Eco-Tec/FrosTool/3D-Model/Node/Case_FrossTool.fcstd

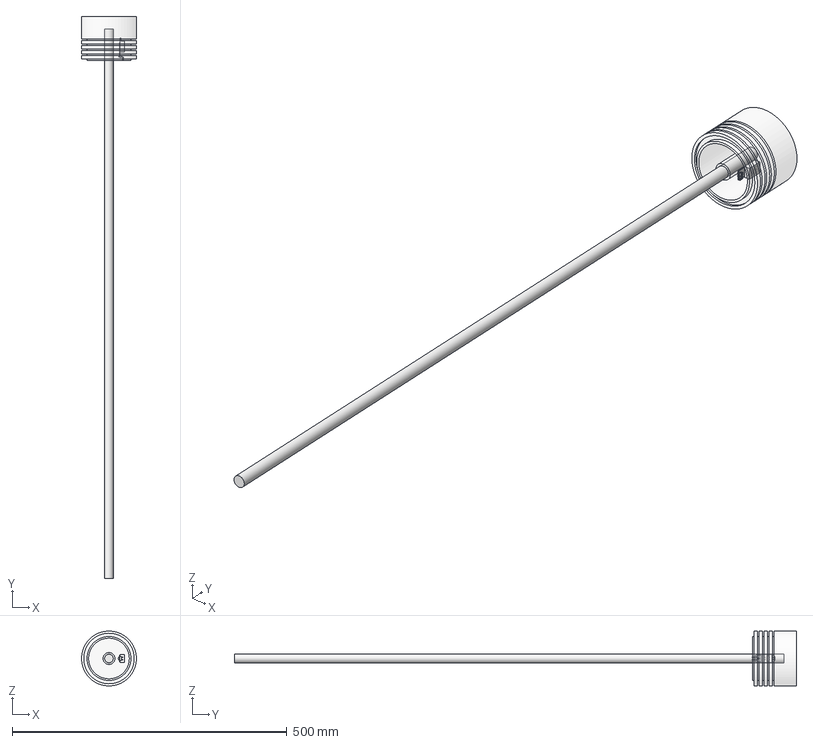
[picture p17: CAD file, 2017-10-28]
3D-Model/Node/Case_FrossTool.fcstd
99.9 x 1023.0 x 100.0 mm
DHT22-by_Gistroy
Tubo 1/2
case1
