Eco-Tec/FrosTool/3D-Model/Parts/Broker/orange-pi-zero-v1-1-1-carly_mx.2/Orange Pi Zero v1_1/parts/PLS-01.SLDPRT

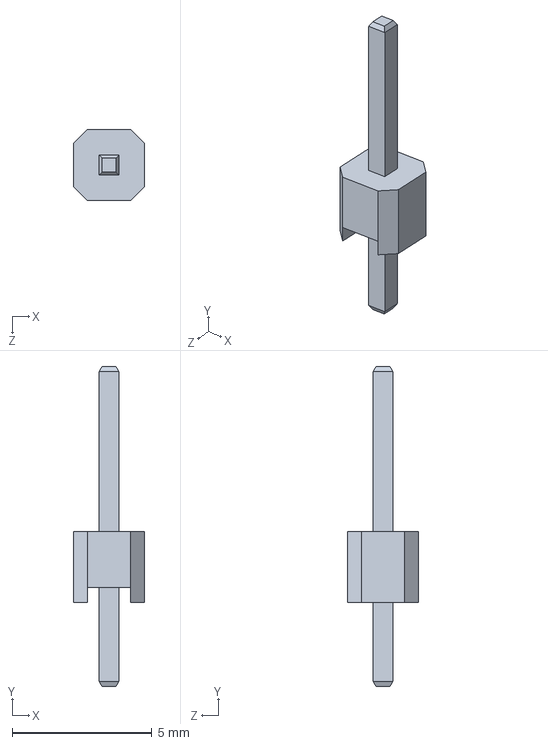
[picture p18: CAD file, 2017-09-27]
3D-Model/Parts/Broker/orange-pi-zero-v1-1-1-carly_mx.2/Orange Pi Zero v1_1/parts/PLS-01.SLDPRT
2.54 x 11.4 x 2.54 mm
