Eco-Tec/FrosTool/3D-Model/Node/FrosTool_ESP8266.FCStd

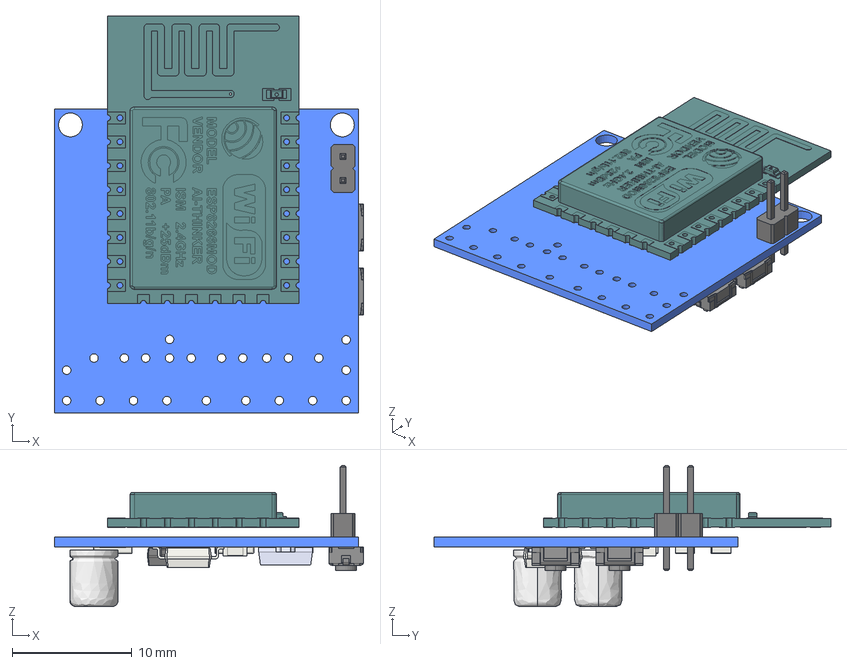
[picture p19: CAD file, 2017-10-22]
3D-Model/Node/FrosTool_ESP8266.FCStd
25.8 x 33.2 x 11.8 mm
PCB_0.8mm
Pin_Header_Straight_1x02_Pitch200mm_
R_1206_
User_Library-Pushbutton3x4x2_sp_
User_Library-Pushbutton3x4x2_sp_001
C_0805_
C_0805_001
SOT_23_
R_1206_001
R_1206_002
R_1206_003
R_1206_004
R_1206_005
R_1206_006
R_1206_007
R_1206_008
Shapes_001
SOIC-8_3.9x4.9mm_Pitch1.27mm_
c_elec_4x5.3_
c_elec_4x5.3_001
