Eco-Tec/FrosTool/3D-Model/Parts/Broker/orange-pi-zero-v1-1-1-carly_mx.2/Orange Pi Zero v1_1/parts/PLD-13.SLDPRT

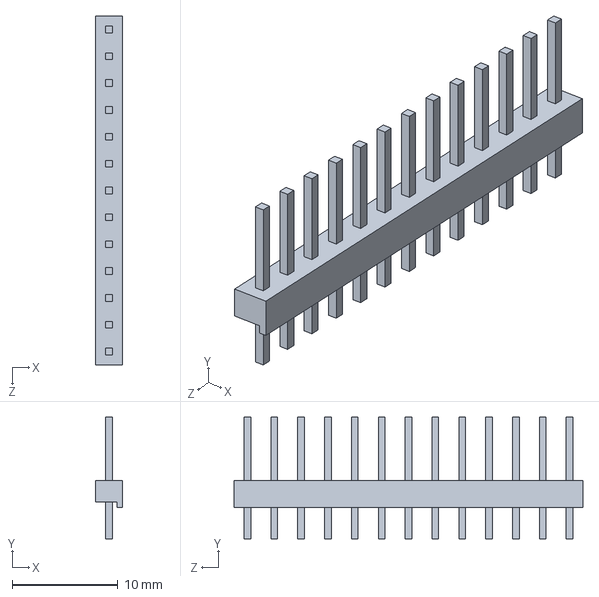
[picture p20: CAD file, 2017-09-27]
3D-Model/Parts/Broker/orange-pi-zero-v1-1-1-carly_mx.2/Orange Pi Zero v1_1/parts/PLD-13.SLDPRT
2.54 x 11.5 x 33.0 mm
