Eco-Tec/FrosTool/3D-Model/Node/Node_1.stl

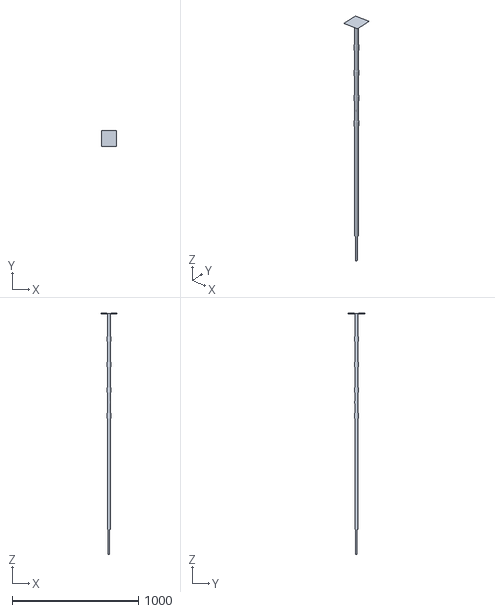
[picture p21: CAD file, 2017-10-08]
3D-Model/Node/Node_1.stl
120.5 x 130.5 x 1912.3
