Eco-Tec/FrosTool/3D-Model/Parts/Broker/orange-pi-zero-v1-1-1-carly_mx.2/Orange Pi Zero v1_1/parts/MicroUSB-B_Molex_105017-0001.SLDPRT

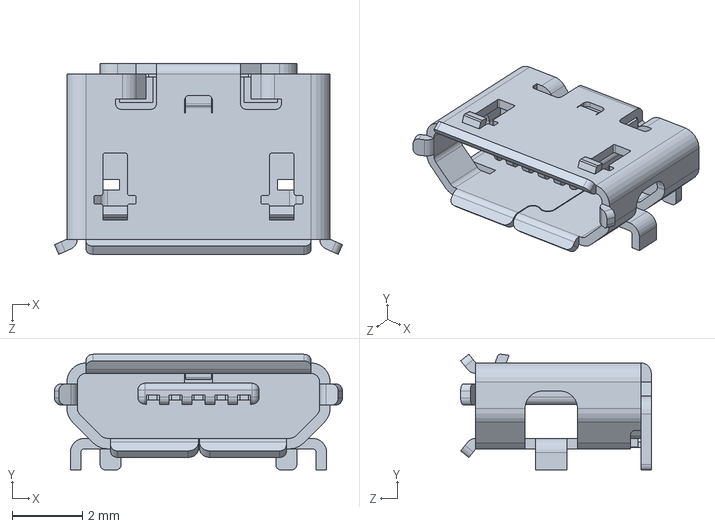
[picture p22: CAD file, 2017-09-27]
3D-Model/Parts/Broker/orange-pi-zero-v1-1-1-carly_mx.2/Orange Pi Zero v1_1/parts/MicroUSB-B_Molex_105017-0001.SLDPRT
8.20 x 3.30 x 5.43 mm
