Eco-Tec/FrosTool/3D-Model/Node/support_bat.step

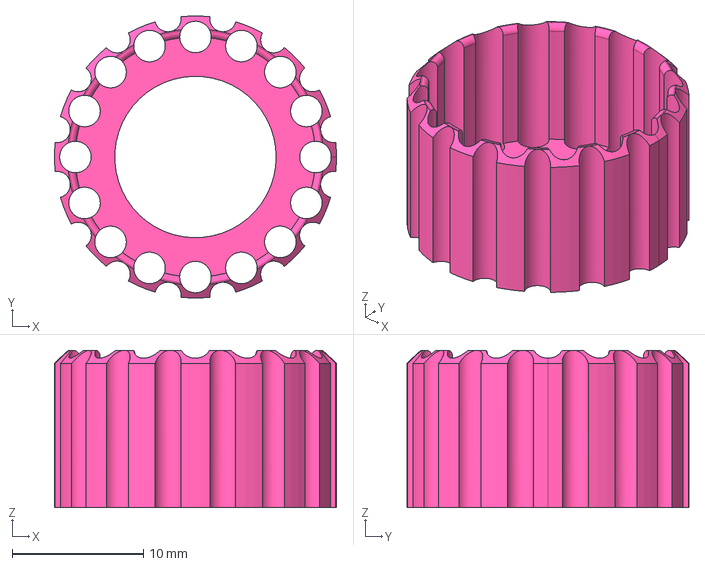
[picture p23: CAD file, 2017-10-08]
3D-Model/Node/support_bat.step
21.5 x 21.5 x 12.0 mm
