Eco-Tec/FrosTool/3D-Model/Parts/Broker/orange-pi-zero-v1-1-1-carly_mx.2/Orange Pi Zero v1_1/parts/Boderboard - Orange Pi zero v1.1.SLDPRT

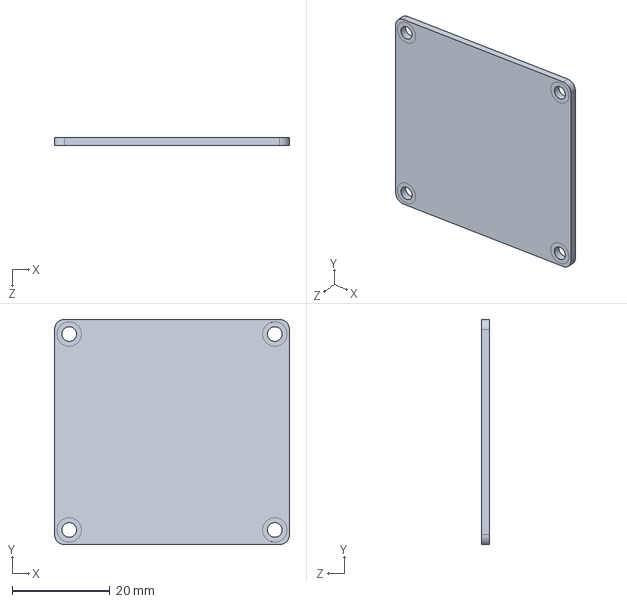
[picture p24: CAD file, 2017-09-27]
3D-Model/Parts/Broker/orange-pi-zero-v1-1-1-carly_mx.2/Orange Pi Zero v1_1/parts/Boderboard - Orange Pi zero v1.1.SLDPRT
48.0 x 46.0 x 1.62 mm
