Eco-Tec/FrosTool/3D-Model/Node/Node.fcstd

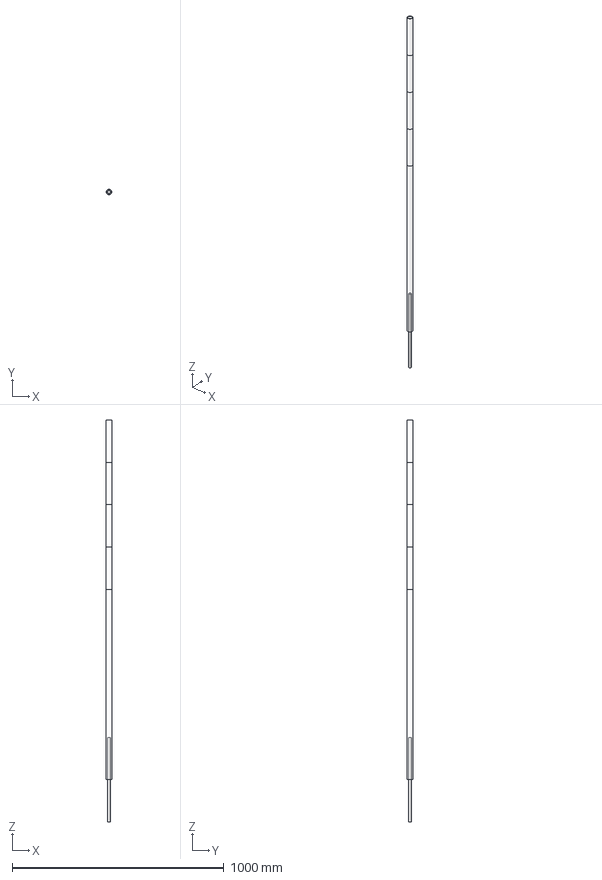
[picture p25: CAD file, 2017-09-27]
3D-Model/Node/Node.fcstd
26.8 x 26.8 x 1900.0 mm
A
B
C
D
E
Cilindro
