Eco-Tec/FrosTool/3D-Model/Parts/Broker/orange-pi-zero-v1-1-1-carly_mx.2/Orange Pi Zero v1_1/parts/User Library-RMS-001L-08A0-GY_body.sldprt

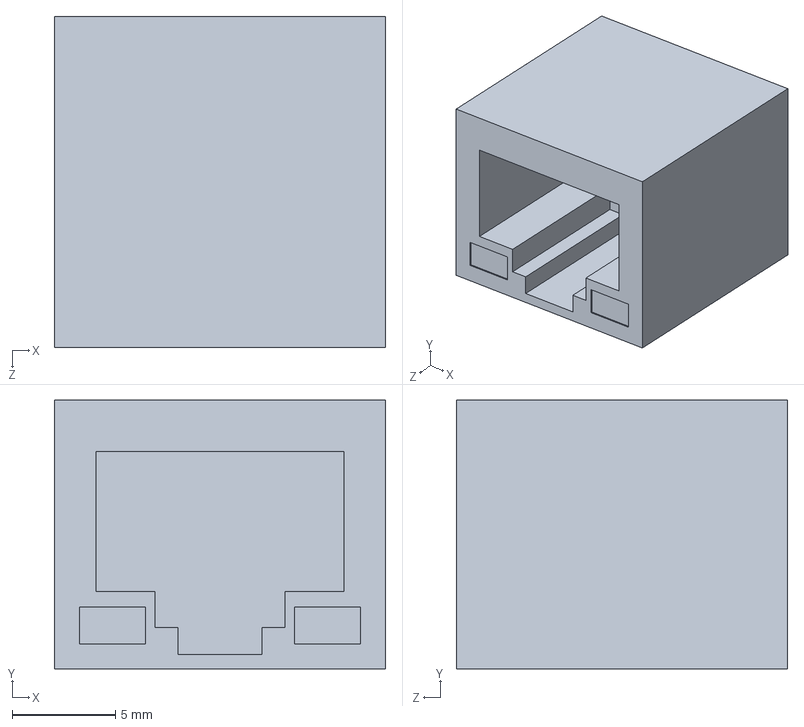
[picture p26: CAD file, 2017-09-27]
3D-Model/Parts/Broker/orange-pi-zero-v1-1-1-carly_mx.2/Orange Pi Zero v1_1/parts/User Library-RMS-001L-08A0-GY_body.sldprt
16.0 x 13.0 x 16.0 mm
