Eco-Tec/FrosTool/Software/Node-ESP8266/config.py

CONFIG = b""
PASSWORD = b"/*Casa*/"
BROKER = b"192.168.31.16" 
SSID = b"Koen"
TOPIC1 = b"/cultivo/temp"
TOPIC2 = b"/cultivo/hum"
TOPIC3 = b"/sensor1/set/temp"
TOPIC4 = b"/sensor1/set/hum"
TOPIC5 = b"/sensor1/alarma"
